Gabse/DMX2PMX/Doku/20190426_003112.jpg

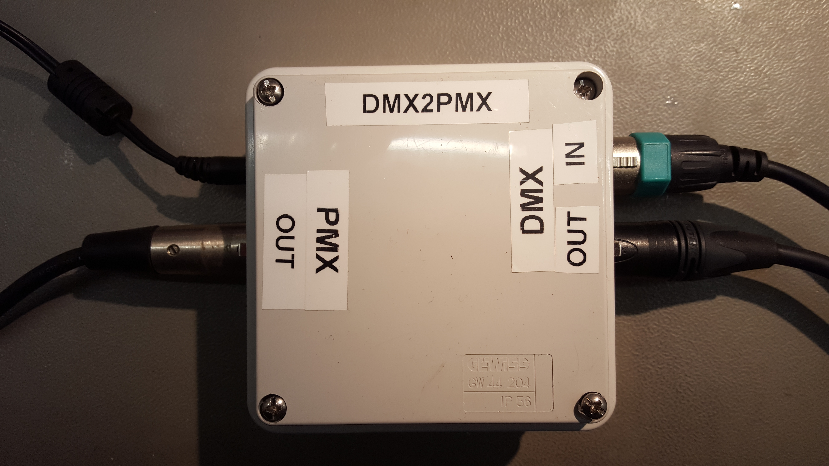
Doku/20190426_003112.jpg
