Gabse/DMX2PMX/Doku/20190426_003235.jpg

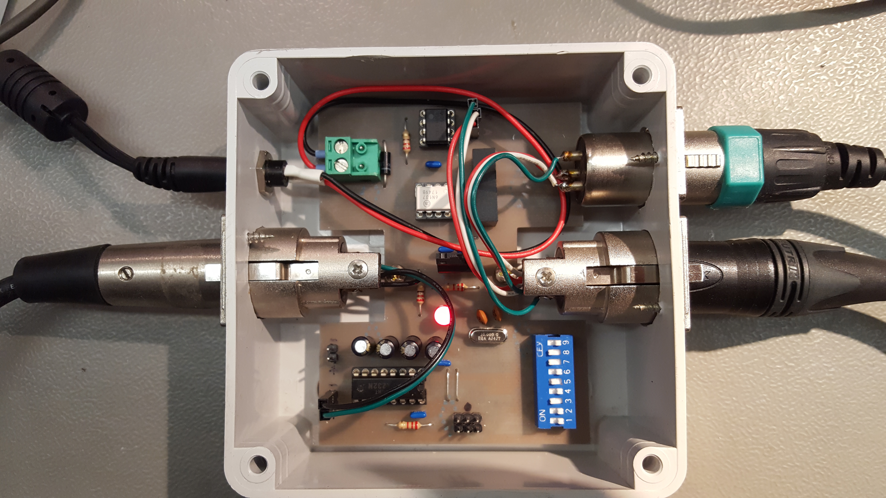
Doku/20190426_003235.jpg
