Gabse/DMX2PMX/Doku/20190426_003246.jpg

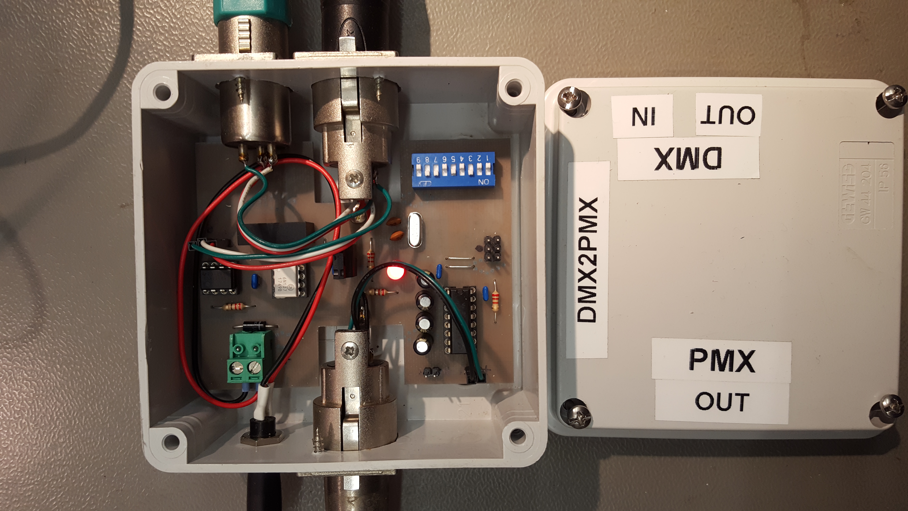
Doku/20190426_003246.jpg
